DaAwesomeP/prox-sense/boards/prox-sense-single-mtch105-v0.1/out/prox-sense-single-mtch105-v0.1.png

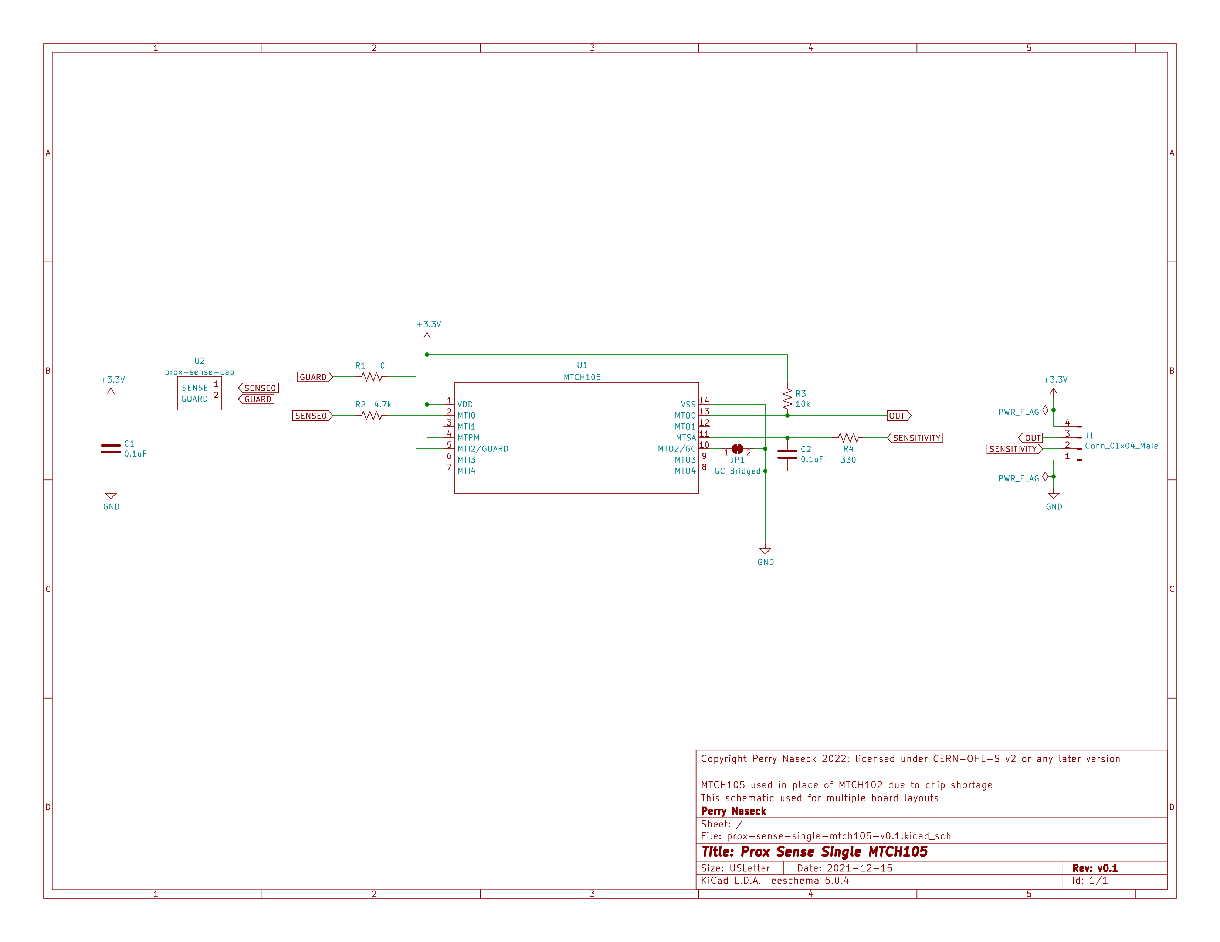
boards/prox-sense-single-mtch105-v0.1/out/prox-sense-single-mtch105-v0.1.png
