DaAwesomeP/prox-sense/boards/prox-sense-single-mtch105-v0.1/prox-sense-single-mtch105-omni-v0.1-19.05mm-handsolder/out/prox-sense-single-mtch105-omni-v0.1-19.05mm-handsolder_3d-side-right_osh_white.png

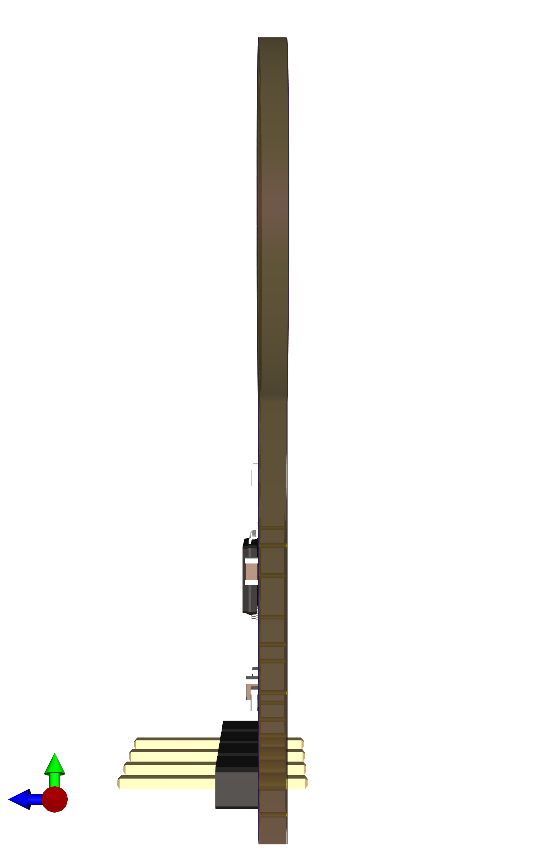
boards/prox-sense-single-mtch105-v0.1/prox-sense-single-mtch105-omni-v0.1-19.05mm-handsolder/out/prox-sense-single-mtch105-omni-v0.1-19.05mm-handsolder_3d-side-right_osh_white.png
